BnZel/NixOS_CyberDeck/cad/v1/kicad/preview_images/V1_PCB_output.jpg

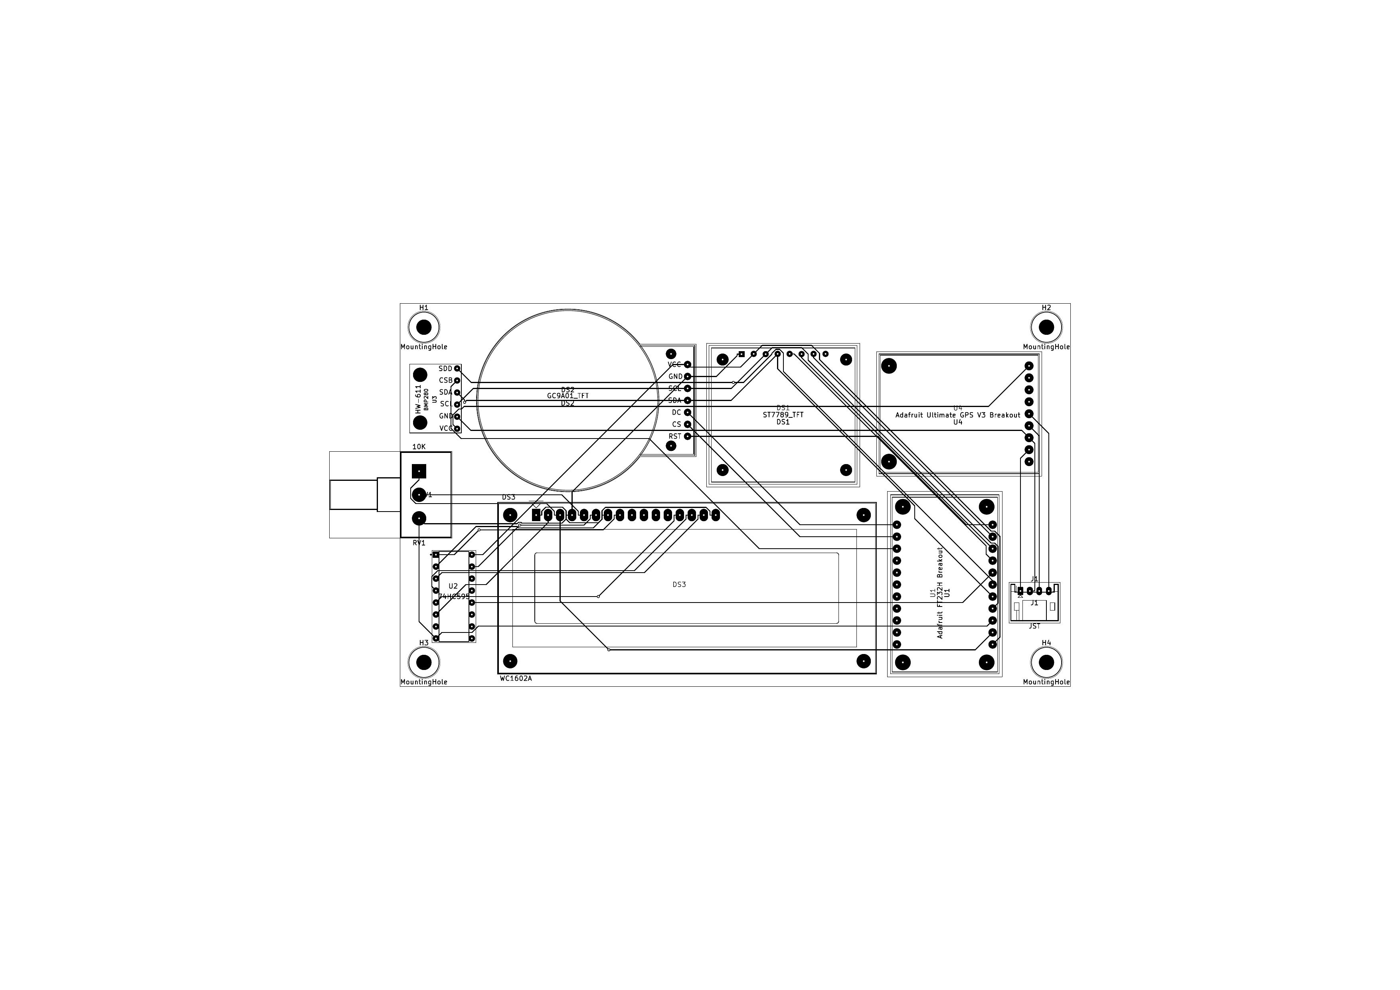
cad/v1/kicad/preview_images/V1_PCB_output.jpg
