BnZel/NixOS_CyberDeck/cad/v1/kicad/schematics/V1_nixos_cyberdeck.kicad_sch

## KiCad design cad/v1/kicad/schematics/V1_nixos_cyberdeck.kicad_sch (2026-07-18)

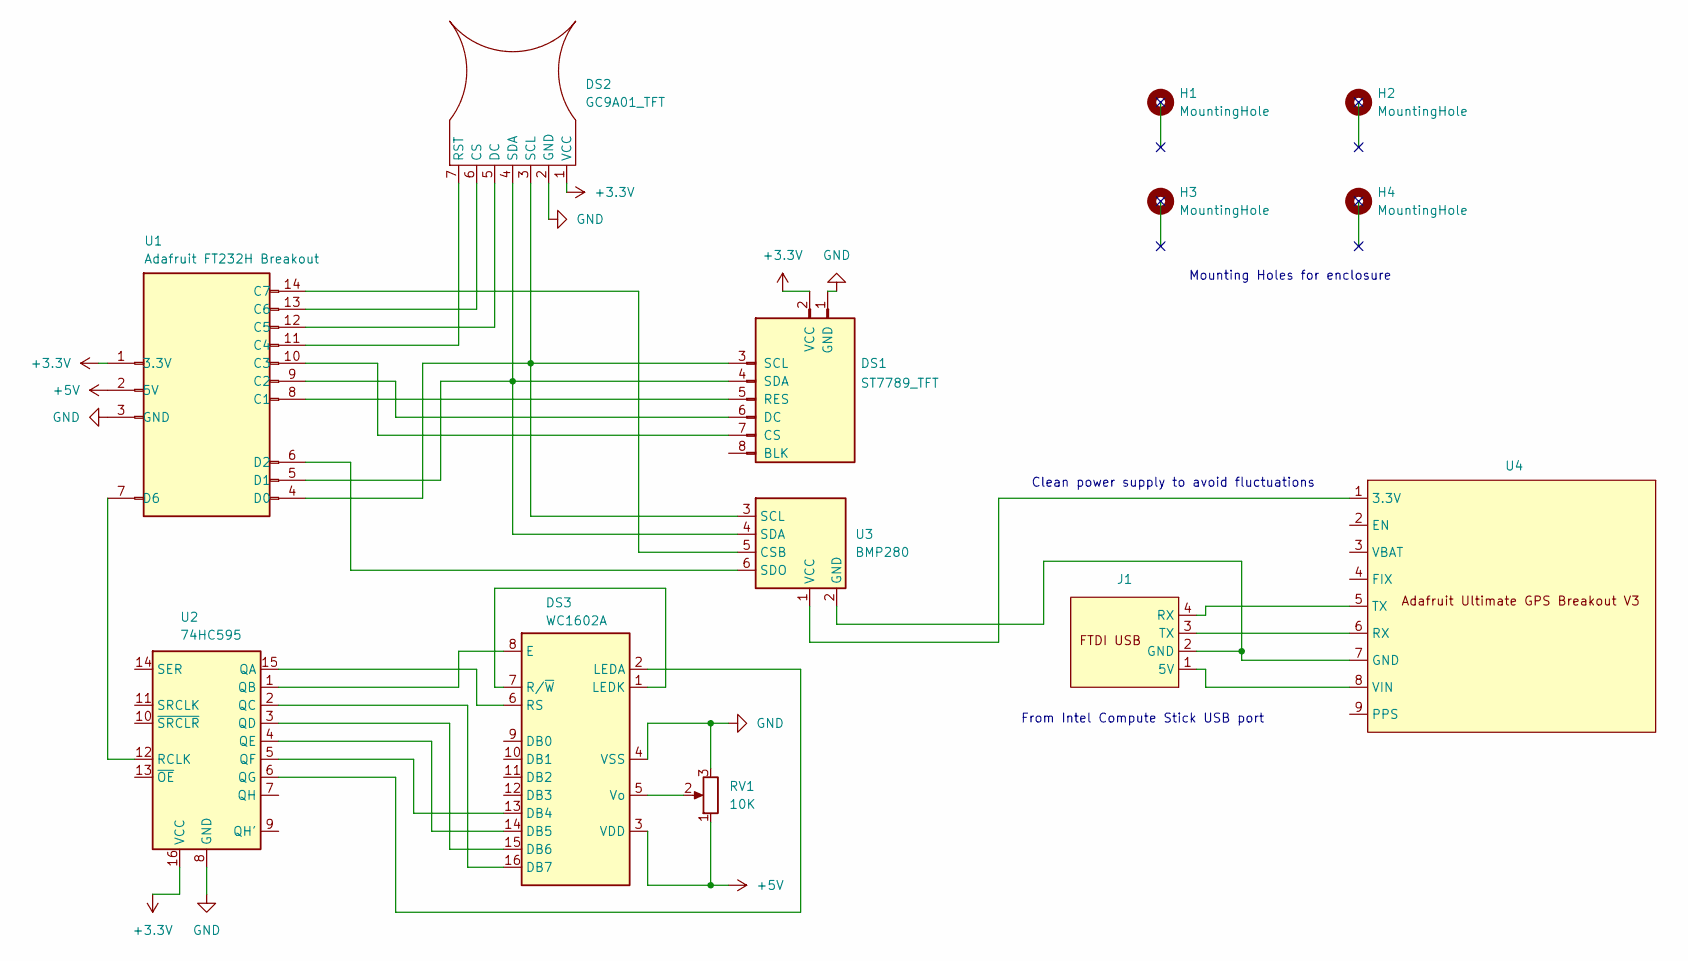
[picture p36: schematic V1_nixos_cyberdeck.kicad_sch]

Parts:
DS1: ST7789_TFT; st7789 TFT
DS2: GC9A01_TFT; GC9A01 TFT
DS3: WC1602A
H1, H2, H3, H4: MountingHole; MountingHole_3.2mm_M3
J1: JST_PH_S4B-PH-K_1x04_P2.00mm_Horizontal
RV1: 10K; Potentiometer_3_PIN
U1: Adafruit FT232H Breakout; USB_C_FT232H
U2: 74HC595; THT_74HC595
U3: BMP280
U4: Adafruit Ulitmate GPS Breakout V3

Connections:
+3.3V: DS1.2 (VCC), DS2.1 (VCC), U1.1 (3.3V), U2.16 (VCC)
+5V: DS3.3 (VDD), RV1.1, U1.2 (5V)
GND: DS1.1 (GND), DS2.2 (GND), DS3.4 (VSS), RV1.3, U1.3 (GND), U2.8 (GND)
unnamed: DS1.3 (SCL), DS2.3 (SCL), U1.4 (D0), U3.3 (SCL)
unnamed: DS1.4 (SDA), DS2.4 (SDA), U1.5 (D1), U3.4 (SDA)
unnamed: DS1.5 (RES), U1.8 (C1)
unnamed: DS1.6 (DC), U1.9 (C2)
unnamed: DS1.7 (CS), U1.10 (C3)
unnamed: DS2.5 (DC), U1.12 (C5)
unnamed: DS2.6 (CS), U1.13 (C6)
unnamed: DS2.7 (RST), U1.11 (C4)
unnamed: DS3.1 (LEDK), DS3.7 (R/~W)
unnamed: DS3.2 (LEDA), U2.6 (QG)
unnamed: DS3.5 (Vo), RV1.2
unnamed: DS3.6 (RS), U2.15 (QA)
unnamed: DS3.8 (E), U2.1 (QB)
unnamed: DS3.13 (DB4), U2.5 (QF)
unnamed: DS3.14 (DB5), U2.4 (QE)
unnamed: DS3.15 (DB6), U2.3 (QD)
unnamed: DS3.16 (DB7), U2.2 (QC)
unnamed: J1.1 (5V), U4.8 (VIN)
unnamed: J1.2 (GND), U3.2 (GND), U4.7 (GND)
unnamed: J1.3 (TX), U4.6 (RX)
unnamed: J1.4 (RX), U4.5 (TX)
unnamed: U1.6 (D2), U3.6 (SDO)
unnamed: U1.7 (D6), U2.12 (RCLK)
unnamed: U1.14 (C7), U3.5 (CSB)
unnamed: U3.1 (VCC), U4.1 (3.3V)

Notes on the sheet:
Clean power supply to avoid fluctuations
From Intel Compute Stick USB port
Mounting Holes for enclosure
